bungernut/XeCapLevelMeter/PCB/TIFDC1004Q_Demo/CapLevelSensorTiFDC1004-F_Mask.pdf

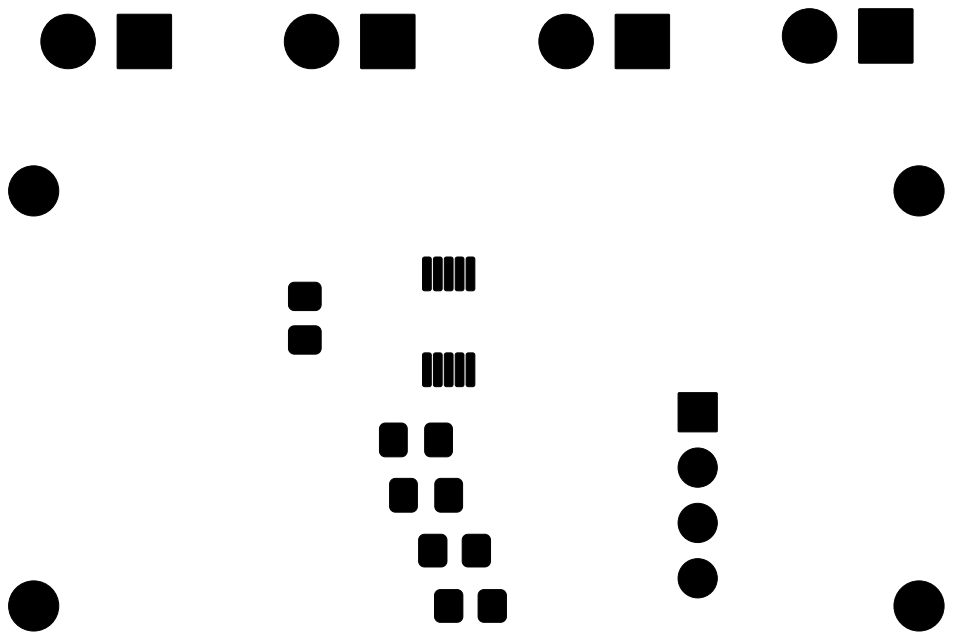
[picture p10: page 1]
