bungernut/XeCapLevelMeter/PCB/TIFDC1004Q_Demo/CapLevelSensorTiFDC1004-F_Paste.pdf

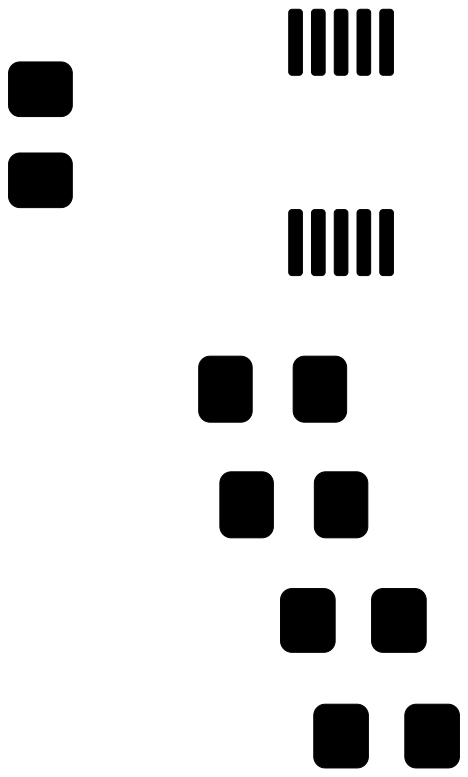
[picture p11: page 1]
