bungernut/XeCapLevelMeter/PCB/TIFDC1004Q_Demo/CapLevelSensorTiFDC1004-F_SilkS.pdf

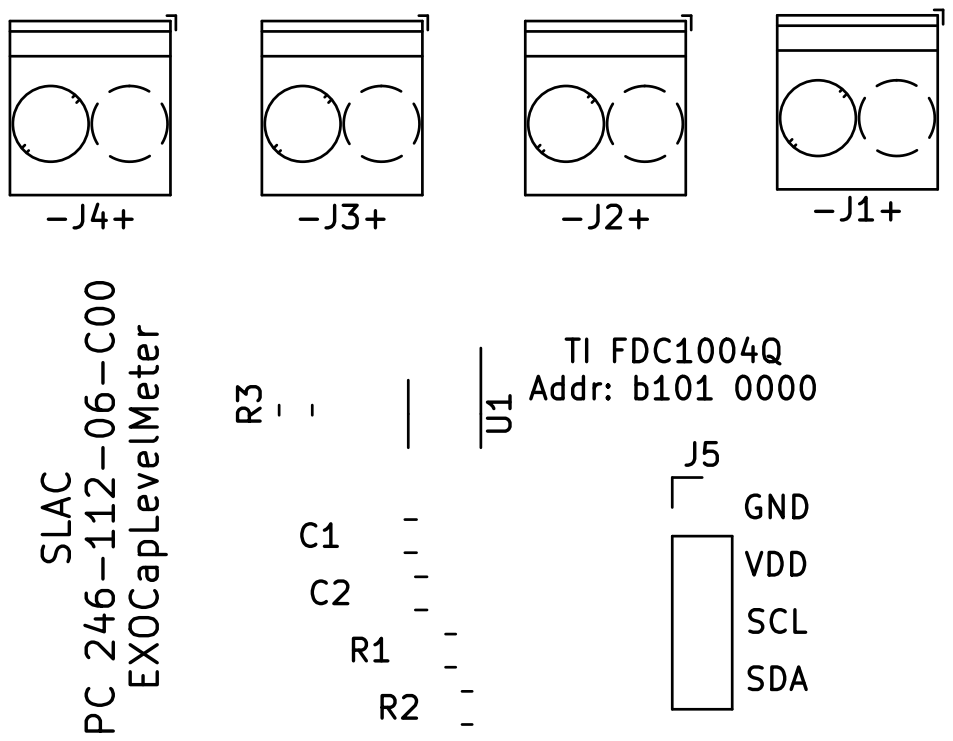
[picture p12: page 1]
